GLGPrograms/tinyDiskII/firmware/src/clock.cpp

#include <avr/io.h>

#include "clock.h"

// Set up PLL driven by internal 2MHz oscillator using 32kHz DFLL reference
void clk_init()
{
  /** DFLL calibration setup **/
  // Enable the internal 32KHz oscillator for DFLL reference
  OSC.CTRL |= OSC_RC32KEN_bm;
  while (!(OSC.STATUS & OSC_RC32KRDY_bm))
    ; // Wait for stabilization
  // Enable DFLL
  DFLLRC2M.CTRL = DFLL_ENABLE_bm;

  /** PLL setup **/
  // Apply multiplying factor
  OSC.PLLCTRL = ((F_CPU) / 2e6);
  // Turn on PLL
  OSC.CTRL = OSC_PLLEN_bm;
  while (!(OSC.STATUS & OSC_PLLRDY_bm))
    ; // Is PLL clk rdy to go?

  CCP = CCP_IOREG_gc; // Unlock secure register
  CLK.CTRL = CLK_SCLKSEL_PLL_gc;
}
